miradamkhan/RP2350-Handheld-Game-Console/src/invaders.h

/*
 * invaders.h — Space Invaders game entry point.
 *
 * Call invaders_run() from the main menu to play Space Invaders.
 * The function runs the complete game loop and returns to menu when
 * the player exits from the game-over screen.
 */

#ifndef INVADERS_H
#define INVADERS_H

void invaders_run(void);

#endif /* INVADERS_H */
