miradamkhan/RP2350-Handheld-Game-Console/src/flappy_render.h

/*
 * flappy_render.h — Flappy Bird game entry point.
 *
 * Call flappy_run() from the main menu to play Flappy Bird.
 * The function runs the complete game loop and returns
 * when the user exits back to the main menu.
 */

#ifndef FLAPPY_RENDER_H
#define FLAPPY_RENDER_H

void flappy_run(void);

#endif /* FLAPPY_RENDER_H */
