miradamkhan/RP2350-Handheld-Game-Console/src/tetris_render.h

/*
 * tetris_render.h — Tetris game entry point.
 *
 * Call tetris_run() from the main menu to play Tetris.
 * The function runs the complete game loop and returns
 * when the user exits back to the main menu.
 */

#ifndef TETRIS_RENDER_H
#define TETRIS_RENDER_H

void tetris_run(void);

#endif /* TETRIS_RENDER_H */
